circuitrocks/Alora-RFM1262/Software/Using_SX126x_Arduino/ArduinoIDE/PingPong/ble.ino

#include <bluefruit.h>

void startAdv(void);
void connect_callback(uint16_t conn_handle);
void disconnect_callback(uint16_t conn_handle, uint8_t reason);

// OTA DFU service
BLEDfu bledfu;
// UART service
BLEUart bleuart;

bool bleUARTisConnected = false;

void initBLE(void)
{
	Bluefruit.begin();
	// Set max power. Accepted values are: -40, -30, -20, -16, -12, -8, -4, 0, 4
	Bluefruit.setTxPower(4);
	Bluefruit.setName("PPG_LORA_SX126x_TEST");

	Bluefruit.autoConnLed(false);

	Bluefruit.Periph.setConnectCallback(connect_callback);
	Bluefruit.Periph.setDisconnectCallback(disconnect_callback);

	// To be consistent OTA DFU should be added first if it exists
	bledfu.begin();

	// Configure and Start BLE Uart Service
	bleuart.begin();

	// Set up and start advertising
	startAdv();
}

void startAdv(void)
{
	// Advertising packet
	Bluefruit.Advertising.addFlags(BLE_GAP_ADV_FLAGS_LE_ONLY_GENERAL_DISC_MODE);
	Bluefruit.Advertising.addTxPower();
	Bluefruit.Advertising.addName();

	/* Start Advertising
   * - Enable auto advertising if disconnected
   * - Interval:  fast mode = 20 ms, slow mode = 152.5 ms
   * - Timeout for fast mode is 30 seconds 
   * - Start(timeout) with timeout = 0 will advertise forever (until connected)
   * 
   * For recommended advertising interval
   * https://developer.apple.com/library/content/qa/qa1931/_index.html   
   */
	Bluefruit.Advertising.restartOnDisconnect(true);
	Bluefruit.Advertising.setInterval(32, 244); // in unit of 0.625 ms
	Bluefruit.Advertising.setFastTimeout(30);   // number of seconds in fast mode
	Bluefruit.Advertising.start(0);				// 0 = Don't stop advertising after n seconds
}

// callback invoked when central connects
void connect_callback(uint16_t conn_handle)
{
	(void)conn_handle;
	bleUARTisConnected = true;
}

/**
 * Callback invoked when a connection is dropped
 * @param conn_handle connection where this event happens
 * @param reason is a BLE_HCI_STATUS_CODE which can be found in ble_hci.h
 */
void disconnect_callback(uint16_t conn_handle, uint8_t reason)
{
	(void)conn_handle;
	(void)reason;
	bleUARTisConnected = false;
}
